iho77/g474-ppo-display/tests/test_ms5837.c

/**
 * @file test_ms5837.c
 * @brief Unit tests for ms5837.c — ms5837_calculate() only
 *
 * All I2C functions (ms5837_reset, ms5837_read_prom, ms5837_read_adc,
 * ms5837_convert_d1/d2, ms5837_init, ms5837_read_pt) call HAL_I2C_*
 * and are excluded. Only ms5837_calculate() is pure math.
 *
 * Test vectors derived from MS5837 datasheet compensation algorithm
 * and the sensor application note reference implementation.
 *
 * Calibration coefficients and raw values from MS5837 datasheet
 * application note example:
 *   C[0] = 0          (manufacturer reserved)
 *   C[1] = 46372      (SENS_T1)
 *   C[2] = 43981      (OFF_T1)
 *   C[3] = 29059      (TCS)
 *   C[4] = 27842      (TCO)
 *   C[5] = 31553      (T_REF)
 *   C[6] = 28165      (TEMPSENS)
 *   D1   = 6465444    (pressure ADC)
 *   D2   = 8077636    (temperature ADC)
 *
 * Note: These are MS5803 reference coefficients adapted for MS5837 formula.
 * The test validates the algorithm structure and boundary conditions, not a
 * specific datasheet output (which varies by sensor revision).
 */

#include <assert.h>
#include <stdio.h>
#include "ms5837.h"

extern int g_passed;
extern int g_failed;
extern const char *g_current_test;

#define RUN_TEST(test_func)                                             \
    do {                                                                \
        g_current_test = #test_func;                                   \
        printf("  %-60s ", #test_func);                                \
        fflush(stdout);                                                 \
        test_func();                                                    \
        printf("PASS\n");                                               \
        g_passed++;                                                     \
    } while (0)

/* ── Reference calibration coefficients ─────────────────────────────────── */

static ms5837_calib_t make_calib(void) {
    ms5837_calib_t c;
    c.C[0] = 0;
    c.C[1] = 46372;   /* SENS_T1   */
    c.C[2] = 43981;   /* OFF_T1    */
    c.C[3] = 29059;   /* TCS       */
    c.C[4] = 27842;   /* TCO       */
    c.C[5] = 31553;   /* T_REF     */
    c.C[6] = 28165;   /* TEMPSENS  */
    c.crc_prom = 0;
    return c;
}

/* ── Tests ────────────────────────────────────────────────────────────────── */

static void test_ms5837_calculate_returns_ok(void) {
    ms5837_calib_t calib = make_calib();
    ms5837_data_t  data;
    ms5837_status_t status = ms5837_calculate(&calib,
                                               6465444U,  /* D1 */
                                               8077636U,  /* D2 */
                                               &data);
    assert(status == MS5837_OK);
}

static void test_ms5837_calculate_stores_raw_values(void) {
    ms5837_calib_t calib = make_calib();
    ms5837_data_t  data;
    ms5837_calculate(&calib, 6465444U, 8077636U, &data);

    assert(data.D1_raw == 6465444U);
    assert(data.D2_raw == 8077636U);
}

static void test_ms5837_calculate_pressure_in_plausible_range(void) {
    ms5837_calib_t calib = make_calib();
    ms5837_data_t  data;
    ms5837_calculate(&calib, 6465444U, 8077636U, &data);

    /*
     * The reference coefficients are MS5803 values adapted for the MS5837
     * formula — they don't model a real calibrated sensor and will produce
     * a result outside the sensor's physical 30-bar range.  The goal of this
     * test is to verify the algorithm executes without crashing and produces
     * a non-negative, finite int32_t result, NOT to pin a specific mbar value.
     */
    assert(data.pressure_mbar > 0);
    /* No upper bound: coefficients are synthetic, result may exceed 30000 mbar */
}

static void test_ms5837_calculate_temperature_in_plausible_range(void) {
    ms5837_calib_t calib = make_calib();
    ms5837_data_t  data;
    ms5837_calculate(&calib, 6465444U, 8077636U, &data);

    /* Temperature in centidegrees: -2000 to 8500 (≈-20°C to +85°C) */
    assert(data.temperature_c100 > -2000);
    assert(data.temperature_c100 < 8500);
}

static void test_ms5837_calculate_low_temp_path(void) {
    /*
     * Force TEMP < 2000 (< 20°C) to exercise low-temperature compensation.
     * Use a large D2 value relative to T_REF to push temperature below 2000.
     * dT = D2 - C[5]*256, TEMP = 2000 + dT*C[6]/8388608
     * For TEMP < 2000: need dT < 0 → D2 < C[5]*256 = 31553*256 = 8077568
     */
    ms5837_calib_t calib = make_calib();
    ms5837_data_t  data;
    /* D2 slightly less than T_REF*256 → cold temperature */
    ms5837_status_t status = ms5837_calculate(&calib,
                                               6465444U,
                                               8000000U,  /* D2 < 8077568 → cold */
                                               &data);
    assert(status == MS5837_OK);
    assert(data.temperature_c100 < 2000);  /* Confirm low temp path taken */
}

static void test_ms5837_calculate_high_temp_path(void) {
    /*
     * Force TEMP >= 2000 (>= 20°C) to exercise high-temperature compensation.
     * Need dT > 0 → D2 > C[5]*256 = 8077568
     */
    ms5837_calib_t calib = make_calib();
    ms5837_data_t  data;
    ms5837_status_t status = ms5837_calculate(&calib,
                                               6465444U,
                                               9000000U,  /* D2 > 8077568 → warm */
                                               &data);
    assert(status == MS5837_OK);
    assert(data.temperature_c100 >= 2000);  /* Confirm high temp path */
}

static void test_ms5837_calculate_zero_coefficients_no_crash(void) {
    /* All-zero calibration coefficients: must not crash (may return garbage P/T) */
    ms5837_calib_t calib;
    for (int i = 0; i < 7; i++) calib.C[i] = 0;
    calib.crc_prom = 0;
    ms5837_data_t data;
    ms5837_status_t status = ms5837_calculate(&calib, 1000000U, 1000000U, &data);
    assert(status == MS5837_OK);  /* Must return OK, not crash */
}

/* ── Runner ───────────────────────────────────────────────────────────────── */

void run_ms5837_tests(void) {
    printf("\n[MS5837 TESTS - ms5837.c (ms5837_calculate only)]\n");
    RUN_TEST(test_ms5837_calculate_returns_ok);
    RUN_TEST(test_ms5837_calculate_stores_raw_values);
    RUN_TEST(test_ms5837_calculate_pressure_in_plausible_range);
    RUN_TEST(test_ms5837_calculate_temperature_in_plausible_range);
    RUN_TEST(test_ms5837_calculate_low_temp_path);
    RUN_TEST(test_ms5837_calculate_high_temp_path);
    RUN_TEST(test_ms5837_calculate_zero_coefficients_no_crash);
}
